Bluescreen2001/ZX81-PCB/Original_photos/board_top_s.jpg

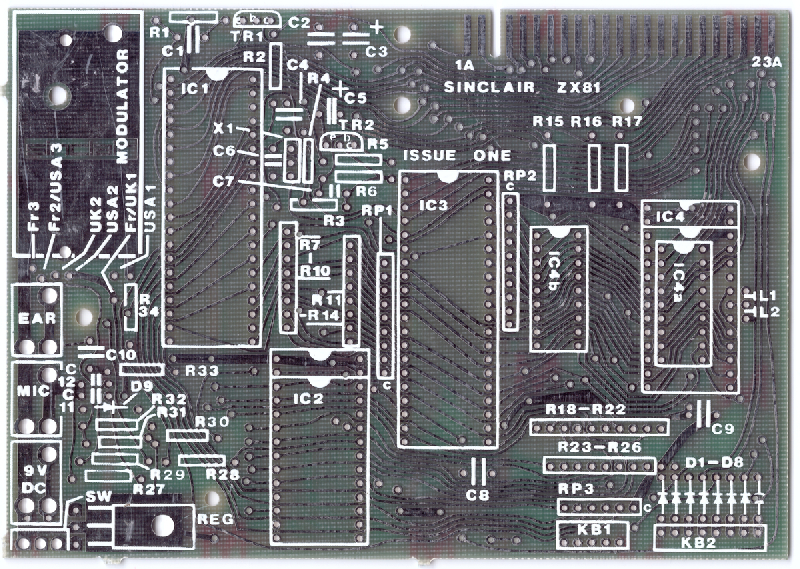
Original_photos/board_top_s.jpg
