Bluescreen2001/ZX81-PCB/ZX81_keyboard/sinclair_zx81_keyboard.jpg

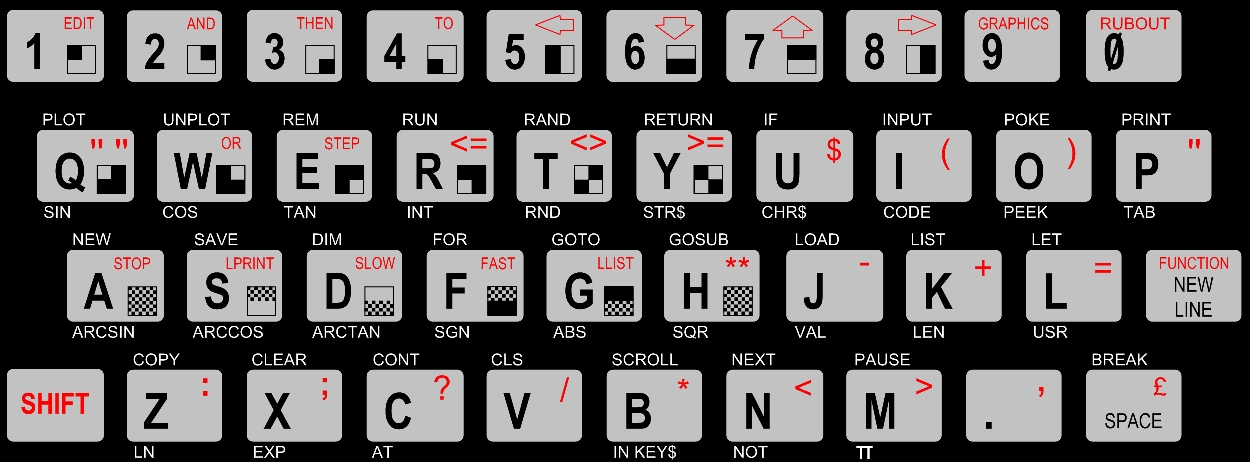
ZX81_keyboard/sinclair_zx81_keyboard.jpg
