Bluescreen2001/ZX81-PCB/ZX81_keyboard/zx81keyboard.png

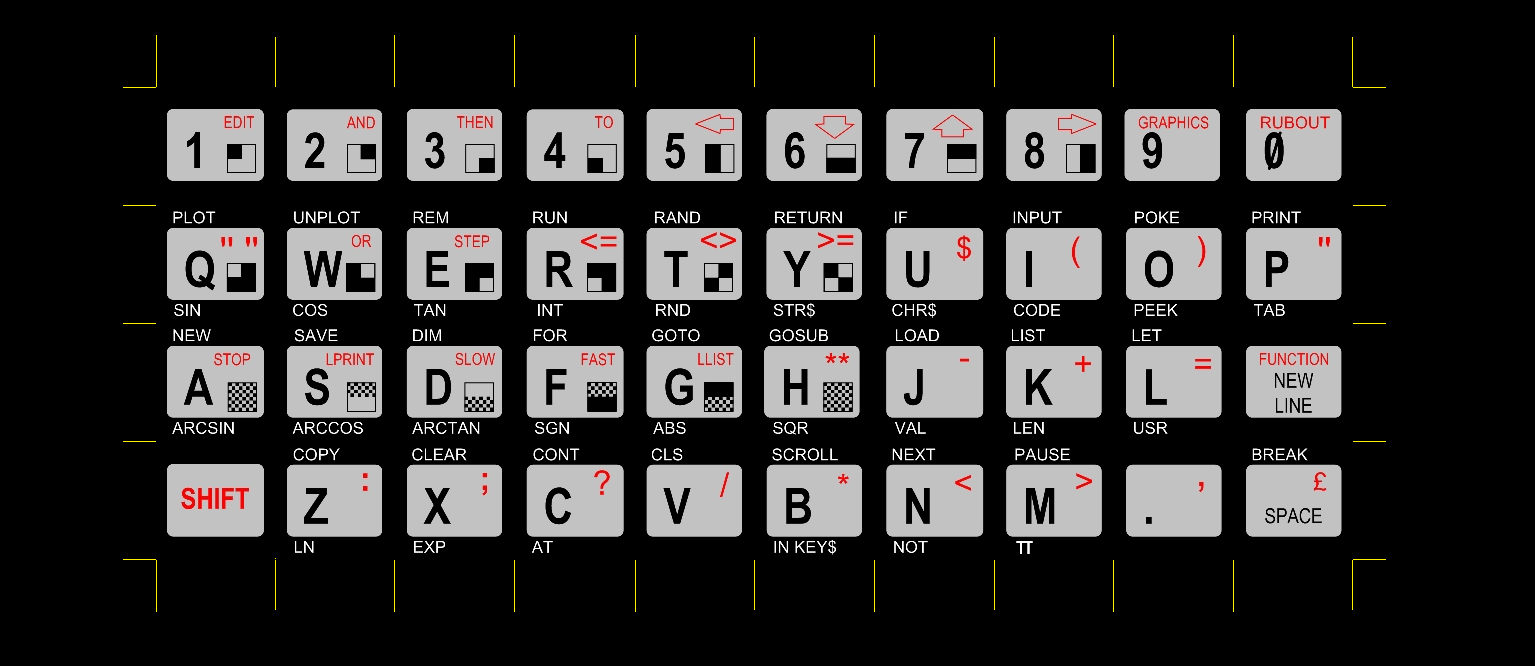
ZX81_keyboard/zx81keyboard.png
