Bluescreen2001/ZX81-PCB/ZX81b/zx81b-pcb.png

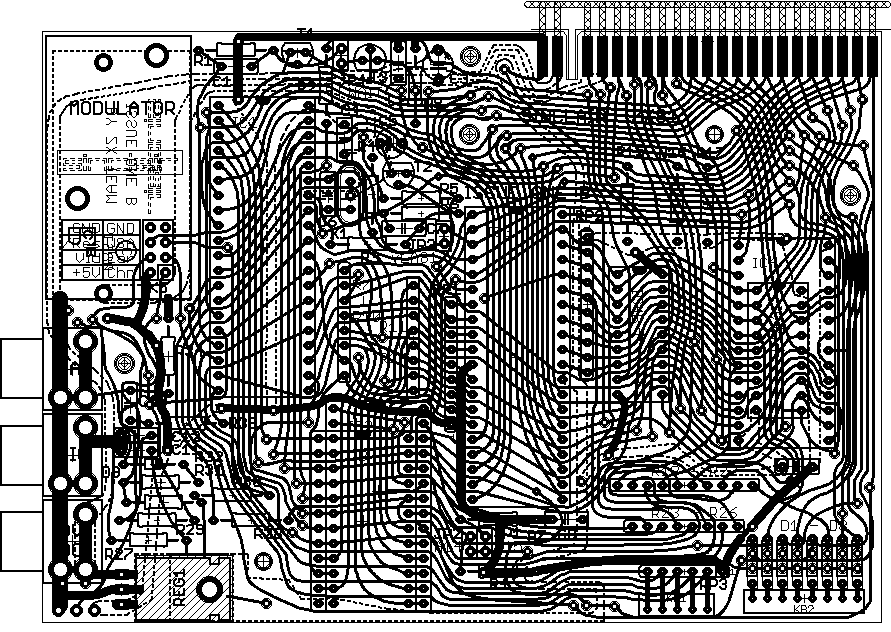
ZX81b/zx81b-pcb.png
