Bluescreen2001/ZX81-PCB/Docs/Issue 1a.png

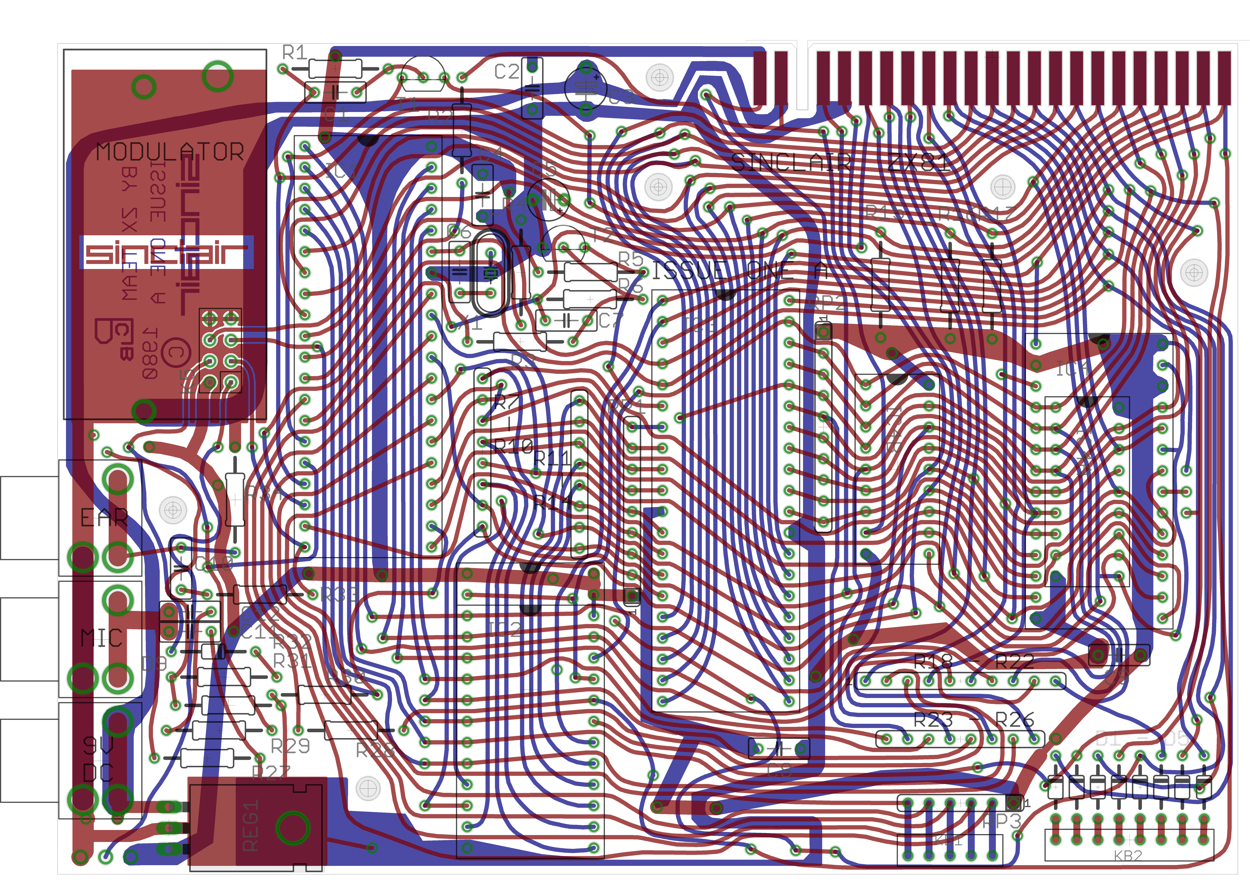
Docs/Issue 1a.png
